francois-berder/iot-heater/heater_firmware/uncommissioned.cpp

#include "board.h"
#include "uncommissioned.h"
#include "settings.h"
#include "Arduino.h"
#include "Ticker.h"
#include "uptime_formatter.h"
#include "version.h"
#include "webpages.h"
#include <DNSServer.h>
#include <ESP8266WiFi.h>
#include <ESPAsyncTCP.h>
#include <ESPAsyncWebServer.h>

#define BUTTON_PRESS_TIMEOUT  (10000)   /* Timeout in milliseconds */
#define JOIN_NETWORK_TIMEOUT  (10000)   /* Timeout in milliseconds */

#define DNS_PORT              (53)

static char webpage_buffer[2048];
static AsyncWebServer server(80);
static DNSServer dns_server;

static bool button_pressed;
static unsigned long button_pressed_start;

static bool joining_wifi_network;
static String device_name;
static String wifi_ssid;
static String wifi_password;
static String basestation_addr;
static unsigned long joining_wifi_network_start;

static bool check_params(void)
{
    if (device_name.length() >= 31
    ||  wifi_ssid.length() >= 63
    ||  wifi_password.length() >= 63
    ||  basestation_addr.length() >= 31)
        return false;

    if (device_name.length() == 0 || wifi_ssid.length() == 0 || basestation_addr.length() == 0)
        return false;

    for (int i = 0; i < device_name.length(); ++i) {
        bool is_char_valid = (device_name[i] >= 'a' && device_name[i] <= 'z')
                          || (device_name[i] >= 'A' && device_name[i] <= 'Z')
                          || (device_name[i] >= '0' && device_name[i] <= '9');
        if (!is_char_valid)
            return false;
    }

    return true;
}

void setup_uncommissioned(void)
{
    pinMode(LED1_PIN, OUTPUT);
    digitalWrite(LED1_PIN, 1);
    pinMode(BUTTON_PIN, INPUT_PULLUP);

    /*
     * Do not rely on external pull-up/pull-down to set
     * the heater state.
     * Force heater in DEFROST mode while in uncommissioning
     * mode.
     */
    pinMode(POSITIVE_OUTPUT_PIN, INPUT);
    pinMode(NEGATIVE_OUTPUT_PIN, INPUT);

    /* Create Wifi AP */
    byte mac[6];
    WiFi.macAddress(mac);
    char ssid[32];
    sprintf(ssid, "heater-%02X%02X%02X%02X%02X%02X",
            mac[0], mac[1], mac[2], mac[3], mac[4], mac[5]);
    char password[32];
    sprintf(password, "%02X%02X%02X%02X%02X%02X",
            mac[0], mac[1], mac[2], mac[3], mac[4], mac[5]);
    IPAddress apIP(192, 168, 1, 1);
    WiFi.mode(WIFI_AP);
    WiFi.softAPConfig(apIP, apIP, IPAddress(255, 255, 255, 0));
    WiFi.softAP(ssid, password);

    Serial.print("Starting WiFi network: ");
    Serial.println(ssid);

    /* Start DNS server */
    dns_server.start(DNS_PORT, "www.heater.local", apIP);

    /* Spawn web server */
    server.on("/", HTTP_GET, [](AsyncWebServerRequest *request){
            byte mac[6];
            WiFi.softAPmacAddress(mac);

            /* Build webpage */
            sprintf(webpage_buffer, uncommissioned_index_html,
                    ESP.getChipId(),
                    FW_VERSION,
                    mac[0], mac[1], mac[2], mac[3], mac[4], mac[5],
                    uptime_formatter::getUptime().c_str());
            request->send_P(200, "text/html", webpage_buffer);
        }
    );

    server.on("/register", HTTP_POST, [] (AsyncWebServerRequest *request) {
      if (request->hasParam("name", true)
      &&  request->hasParam("ssid", true)
      &&  request->hasParam("password", true)) {
        /* Attempt to join SSID/Password */
        if (!joining_wifi_network) {
            device_name = request->getParam("name", true)->value();
            wifi_ssid = request->getParam("ssid", true)->value();
            wifi_password = request->getParam("password", true)->value();
            basestation_addr =  request->getParam("basestation", true)->value();
            if (check_params()) {
                joining_wifi_network_start = millis();
                joining_wifi_network = true;
            } else {
                request->send_P(200, "text/html", webpage_buffer);
            }
        }
    } else {
        request->send_P(200, "text/html", webpage_buffer);
      }
    }
    );
    server.begin();
}

void loop_uncommissioned(void)
{
    /* Blink LED if someone connected to AP */
    {
        static unsigned long counter = 0;
        if (wifi_softap_get_station_num() == 0) {
          digitalWrite(LED1_PIN, 1);
          counter = 0;
        } else {
          if (millis() - counter > 100) {
              digitalWrite(LED1_PIN, !digitalRead(LED1_PIN));
              counter = millis();
          }
        }
    }

    /* Clear configuration if button is pressed for a while */
    if (digitalRead(BUTTON_PIN) == 0) {
        if (!button_pressed) {
            button_pressed = true;
            button_pressed_start = millis();
        } else if (millis() - button_pressed_start >= BUTTON_PRESS_TIMEOUT) {
            settings_erase();
            ESP.restart();
        }
    } else {
        button_pressed = false;
    }

    if (joining_wifi_network) {
        server.end();
        dns_server.stop();
        Serial.print("Joining network ");
        Serial.println(wifi_ssid);
        WiFi.mode(WIFI_STA);
        WiFi.begin(wifi_ssid, wifi_password);
        while (WiFi.status() != WL_CONNECTED && (millis() - joining_wifi_network_start) < JOIN_NETWORK_TIMEOUT) {
            delay(500);
            Serial.print(".");
        }
        if (WiFi.status() == WL_CONNECTED) {
            settings_create(device_name, wifi_ssid, wifi_password, basestation_addr);
        }
        ESP.restart();
    }

    dns_server.processNextRequest();
}
