francois-berder/iot-heater/base_station/src/sms_sender.hpp

#ifndef SMS_SENDER_HPP
#define SMS_SENDER_HPP

#include <chrono>
#include <cstdint>
#include <map>
#include <mutex>
#include <string>


class SMSSender {
public:
    SMSSender(const SMSSender &l) = delete;
    SMSSender(SMSSender&&) = delete;
    SMSSender& operator=(const SMSSender &l) = delete;
    SMSSender& operator=(SMSSender&&) = delete;

    static SMSSender& instance();

    /**
     * @brief Send SMS
     *
     * @param to phone number
     * @param content
     * @return true SMS sent successfully
     * @return false SMS not sent
     */
    bool sendSMS(const std::string& to, const std::string &content);

    /**
     * @brief Clean old SMS to avoid having too many files
     * in the SMS outgoing directory.
     *
     * This function should periodically be called.
     */
    void cleanupSMS();

private:

    SMSSender();
    ~SMSSender() = default;

    void cleanOutgoingDir();

    std::mutex m_mutex;
    uint64_t m_counter;
    std::map<std::string, std::chrono::time_point<std::chrono::steady_clock>> m_old_files;
};

#endif
