francois-berder/iot-heater/base_station/src/timer.hpp

#ifndef TIMER_HPP
#define TIMER_HPP

class Timer {
public:
    Timer();
    virtual ~Timer();

    void start(unsigned int period_ms, bool periodic = false);
    void stop();

    int getFD() const;

private:
    int fd;
};

#endif
